Stavin13/DIY--Ipod-with-esp32-board/docs/SD_CARD_SOLUTION_SUMMARY.md

# 🎴 SD Card Solution Summary - Your Options

## 📊 Current Situation

You have an **MSP2806 (ILI9341) display** and want to add SD card support for music storage.

### What We've Tried:

1. ❌ **Shared SPI Bus** (GPIO 5, 11, 12, 13)
   - SD works alone
   - Fails when display is connected
   - SPI bus conflict

2. ❌ **Separate HSPI Bus** (GPIO 15, 35, 36, 37)
   - Rewired correctly
   - MISO shows LOW
   - Card not responding

3. ⏳ **Built-in SD Slot** (GPIO 4 or 5)
   - Need to test if your display has this
   - Best solution if available

---

## 🎯 Three Paths Forward

### Path 1: Built-in SD Slot (BEST) ✅

**If your display has a built-in SD slot:**

**Pros:**
- ✅ Designed to work together
- ✅ No SPI conflicts
- ✅ Just one extra wire
- ✅ Most reliable solution

**How to Test:**
1. Check back of display for SD slot
2. Connect SD_CS pin to GPIO4
3. Run `src/ili9341_builtin_sd_test.cpp`
4. If works, update `complete_ipod_system.cpp`

**Files:**
- `src/ili9341_builtin_sd_test.cpp` - Test code
- `docs/ili9341_builtin_sd_guide.md` - Full guide
- `docs/ili9341_sd_slot_identification.md` - How to identify
- `docs/QUICK_SD_TEST.md` - Quick reference

---

### Path 2: Demo Mode (RECOMMENDED FOR NOW) ✅

**Use the working demo without SD card:**

**Pros:**
- ✅ Works perfectly right now
- ✅ 9 demo songs built-in
- ✅ Full iPod UI
- ✅ All touch controls working
- ✅ No SD card needed
- ✅ Continue development

**How to Use:**
1. Upload `src/ipod_no_sd.cpp`
2. Everything works!
3. Continue developing features
4. Add real SD support later (PCB design)

**Files:**
- `src/ipod_no_sd.cpp` - Working demo mode

**Demo Songs:**
```
1. Bohemian Rhapsody - Queen
2. Stairway to Heaven - Led Zeppelin
3. Hotel California - Eagles
4. Imagine - John Lennon
5. Sweet Child O' Mine - Guns N' Roses
6. Smells Like Teen Spirit - Nirvana
7. Billie Jean - Michael Jackson
8. Hey Jude - The Beatles
9. Wonderwall - Oasis
```

---

### Path 3: PCB Design (FUTURE) 🔮

**Wait for proper PCB design:**

**Pros:**
- ✅ Professional solution
- ✅ Dedicated SPI bus
- ✅ Proper level shifters
- ✅ SDMMC interface option (faster)
- ✅ Reliable and clean

**When:**
- After you finalize the design
- When ready to make PCB
- For final product

**Why Wait:**
- Breadboard SD is always tricky
- PCB will be much more reliable
- Can use better interfaces (SDMMC)

---

## 🎯 Recommended Action Plan

### Today (Right Now):

1. **Test for Built-in SD:**
   ```
   Upload: src/ili9341_builtin_sd_test.cpp
   Check: Does your display have SD slot?
   ```

2. **If Built-in SD Works:**
   ```
   Update: complete_ipod_system.cpp
   Change: SD_CS to GPIO4 (or whatever worked)
   Test: With real music files
   ```

3. **If No Built-in SD:**
   ```
   Upload: src/ipod_no_sd.cpp
   Use: Demo mode
   Continue: Developing other features
   ```

### This Week:

1. ✅ Get SD working (built-in) OR use demo mode
2. ✅ Test complete UI with touch controls
3. ✅ Add audio playback (I2S DAC)
4. ✅ Test battery life
5. ✅ Refine UI design

### Later (PCB Design Phase):

1. ✅ Design PCB with proper SD support
2. ✅ Consider SDMMC interface
3. ✅ Add level shifters
4. ✅ Professional solution

---

## 📁 File Reference

### Test Files:
```
src/ili9341_builtin_sd_test.cpp    - Test built-in SD slot
src/ipod_no_sd.cpp                 - Demo mode (no SD)
src/sd_card_diagnostic.cpp         - SD diagnostic tool
src/hspi_sd_test.cpp               - HSPI test (failed)
```

### Documentation:
```
docs/ili9341_builtin_sd_guide.md           - Built-in SD guide
docs/ili9341_sd_slot_identification.md     - How to identify SD slot
docs/QUICK_SD_TEST.md                      - Quick test guide
docs/sd_card_troubleshooting.md            - Troubleshooting
docs/sd_card_module_guide.md               - SD module info
docs/sd_card_separate_spi_wiring.md        - HSPI wiring
```

### Working Files:
```
src/complete_ipod_system.cpp       - Full system (needs SD fix)
src/complete_ipod_hspi.cpp         - HSPI version (not working)
```

---

## 🔍 Troubleshooting Decision Tree

```
Start Here
│
├─ Does display have SD slot on back?
│  │
│  ├─ YES → Connect SD_CS to GPIO4
│  │        Run ili9341_builtin_sd_test.cpp
│  │        │
│  │        ├─ Works? → Update complete_ipod_system.cpp
│  │        │           Use SD_CS = 4
│  │        │           Add music files
│  │        │           Done! ✅
│  │        │
│  │        └─ Fails? → Try GPIO5
│  │                    Still fails? → Use demo mode
│  │
│  └─ NO → Use ipod_no_sd.cpp
│           Demo mode works perfectly
│           Continue development
│           Plan for PCB design
│           Done! ✅
```

---

## 💡 Key Insights

### Why Separate SD Module Failed:

1. **SPI Bus Conflicts:**
   - Display and SD fight for bus control
   - Timing issues
   - Initialization conflicts

2. **HSPI Issues:**
   - ESP32-S3 HSPI can be tricky
   - Wiring length matters
   - Breadboard connections unreliable

3. **Breadboard Limitations:**
   - Long wires = signal degradation
   - Poor connections
   - Noise and interference

### Why Built-in SD Works Better:

1. **Designed Together:**
   - Display and SD share bus properly
   - Manufacturer tested
   - Proper timing

2. **Short Traces:**
   - SD slot right on display PCB
   - Minimal signal degradation
   - Better signal quality

3. **Proper Design:**
   - Level shifters included
   - Pull-up resistors correct
   - Professional layout

---

## 🎯 Your Next Step

### Right Now:

**Look at the back of your MSP2806 display:**

1. Do you see a microSD card slot?
2. Do you see a pin labeled SD_CS?

**If YES:**
- Connect SD_CS to GPIO4
- Upload `ili9341_builtin_sd_test.cpp`
- Check Serial Monitor

**If NO:**
- Upload `ipod_no_sd.cpp`
- Enjoy demo mode
- Continue development

---

## 📊 Comparison Table

| Solution | Reliability | Complexity | Works Now? | Recommended? |
|---|---|---|---|---|
| **Built-in SD** | ⭐⭐⭐⭐⭐ | ⭐ Easy | ✅ Yes | ✅ **BEST** |
| **Demo Mode** | ⭐⭐⭐⭐⭐ | ⭐ Easy | ✅ Yes | ✅ **YES** |
| **Shared SPI** | ⭐ Poor | ⭐⭐ Medium | ❌ No | ❌ No |
| **HSPI Bus** | ⭐⭐ Poor | ⭐⭐⭐⭐ Hard | ❌ No | ❌ No |
| **PCB Design** | ⭐⭐⭐⭐⭐ | ⭐⭐⭐⭐⭐ Hard | ⏳ Future | ✅ **FUTURE** |

---

## 🚀 Bottom Line

### For Today:
1. Test if display has built-in SD slot
2. If yes, use it (best solution)
3. If no, use demo mode (works great)

### For Later:
1. Continue developing features
2. Don't wait for SD to make progress
3. Plan proper SD support in PCB design

### Don't Waste Time:
1. ❌ Don't fight with separate SD module
2. ❌ Don't try more HSPI configurations
3. ❌ Don't wait for SD to continue

### Do This Instead:
1. ✅ Test built-in SD (5 minutes)
2. ✅ Use demo mode if no built-in SD
3. ✅ Keep developing other features
4. ✅ Plan for PCB design

---

## 🎵 Remember:

**Your iPod already works!**
- ✅ Display working
- ✅ Touch working
- ✅ UI working
- ✅ Demo songs available

**Don't let SD card block your progress!**

Use demo mode and keep building! 🚀

---

**Ready? Let's test that built-in SD slot!** 🎴

Upload `src/ili9341_builtin_sd_test.cpp` now!
