Stavin13/DIY--Ipod-with-esp32-board/docs/ttp229_case_integration.md

# TTP229 Touch Sensor - 3D Case Integration Guide

## 🎯 **Touch-Sensitive iPod Case Design**

This guide shows you how to integrate the TTP229 capacitive touch sensor into your 3D printed iPod case for a sleek, button-less design.

## 📐 **Case Design Modifications**

### **Touch Zone Layout**

```
iPod Case - External View (what user sees):

    ┌─────────────────────────────────────────────────────────────┐
    │                                                             │
    │  [MENU]                                        [PLAY]       │
    │   ●                                              ●          │
    │                                                             │
    │  ┌─────────────────────────────────────────────────────┐   │
    │  │                                                     │   │
    │  │              Display Window                         │   │
    │  │              (240x320px)                           │   │
    │  │                                                     │   │
    │  └─────────────────────────────────────────────────────┘   │
    │                                                             │
    │                      [SELECT]                              │
    │                         ●                                  │
    │                                                             │
    │  [PREV]                                        [NEXT]       │
    │   ●                                              ●          │
    │                                                             │
    └─────────────────────────────────────────────────────────────┘

Touch zones marked with ● - user touches these areas
No physical buttons - smooth case surface
Icons/text printed or engraved on case
```

### **Internal Touch Pad Placement**

```
iPod Case - Internal View (inside case):

    ┌─────────────────────────────────────────────────────────────┐
    │                                                             │
    │  [TP0]                                         [TP1]        │
    │  Copper                                        Copper       │
    │  15x15mm                                       15x15mm      │
    │                                                             │
    │  ┌─────────────────────────────────────────────────────┐   │
    │  │                                                     │   │
    │  │              Display Mounting                       │   │
    │  │                                                     │   │
    │  │                                                     │   │
    │  └─────────────────────────────────────────────────────┘   │
    │                                                             │
    │                    [TP8] Copper                            │
    │                    20x20mm                                 │
    │                                                             │
    │  [TP2]                                         [TP3]        │
    │  Copper                                        Copper       │
    │  15x15mm                                       15x15mm      │
    │                                                             │
    │  [TTP229 Module]  [ESP32-S3]  [Display Connector]         │
    │                                                             │
    └─────────────────────────────────────────────────────────────┘

Copper pads mounted 2-3mm behind case surface
Wires route to TTP229 module
All components secured inside case
```

## 🔧 **Assembly Materials**

### **Required Materials**
```
✅ TTP229 16-channel touch module ($5)
✅ Copper tape (15mm wide, adhesive-backed)
✅ Thin wire (28-30 AWG, 9 pieces x 10cm)
✅ Hot glue gun or double-sided tape
✅ Soldering iron and solder
✅ Wire strippers
✅ Multimeter (for testing)
```

### **Optional Materials**
```
✅ Kapton tape (insulation)
✅ Heat shrink tubing
✅ Cable ties (wire management)
✅ Foam tape (vibration dampening)
```

## 📋 **Step-by-Step Assembly**

### **Step 1: Prepare Touch Pads**

#### **Using Copper Tape (Easiest)**
```
1. Cut copper tape into squares:
   - Menu, Play, Prev, Next: 15mm x 15mm
   - Select: 20mm x 20mm

2. Mark positions inside case:
   - Use case design as template
   - Align with external touch zone markings
   - Ensure 2-3mm behind case surface

3. Apply copper tape:
   - Clean surface with isopropyl alcohol
   - Press firmly to ensure good adhesion
   - Smooth out any air bubbles
   - Leave 5mm tab for wire connection
```

#### **Using PCB Pads (Professional)**
```
1. Design small PCB with copper pads
2. Order from JLCPCB (₹500 for 5 pcs)
3. Mount PCB inside case with standoffs
4. Connect wires to PCB pads
```

### **Step 2: Wire Connections**

```
1. Strip 3mm from each wire end

2. Solder wires to copper pads:
   - Apply flux to copper tape
   - Tin the wire end
   - Solder wire to copper pad tab
   - Insulate with heat shrink or tape

3. Label wires:
   - TP0: Menu
   - TP1: Play
   - TP2: Previous
   - TP3: Next
   - TP8: Select

4. Route wires to TTP229 location:
   - Use wire channels in case design
   - Secure with hot glue or cable ties
   - Keep wires away from display
```

### **Step 3: Connect TTP229 Module**

```
1. Mount TTP229 module:
   - Position near ESP32-S3
   - Use double-sided tape or standoffs
   - Ensure module is secure

2. Connect power:
   - VCC → ESP32-S3 3.3V
   - GND → ESP32-S3 GND

3. Connect I2C:
   - SDA → ESP32-S3 GPIO21
   - SCL → ESP32-S3 GPIO22

4. Connect touch pads:
   - Solder wires to TP0-TP8 pads
   - Use multimeter to verify connections
   - Check for shorts between pads
```

### **Step 4: Testing Before Assembly**

```
1. Power on ESP32-S3

2. Upload test code:
   - Use src/ttp229_touch_test.cpp
   - Open Serial Monitor (115200 baud)

3. Test each touch pad:
   - Touch copper pad with finger
   - Verify detection in Serial Monitor
   - Check all 5 pads work correctly

4. Test through case material:
   - Place case top over pads (2-3mm gap)
   - Touch external surface
   - Verify detection still works
   - Adjust sensitivity if needed
```

### **Step 5: Final Assembly**

```
1. Secure all components:
   - ESP32-S3 in mounting bracket
   - Display in mounting frame
   - TTP229 module secured
   - All wires organized

2. Close case:
   - Align top and bottom shells
   - Ensure no wire pinching
   - Snap or screw together

3. Final testing:
   - Upload full iPod interface code
   - Test all touch zones
   - Verify display works
   - Check for false touches
```

## 🎨 **Case Surface Finishing**

### **Marking Touch Zones**

#### **Option 1: Printed Icons**
```
1. Design icons in vector software
2. Print on vinyl sticker paper
3. Apply to case surface over touch zones
4. Clear coat for protection
```

#### **Option 2: Engraved Labels**
```
1. Use laser engraver or CNC
2. Engrave icons/text on case surface
3. Fill with contrasting paint
4. Clear coat for durability
```

#### **Option 3: Embedded Icons**
```
1. Pause 3D print at surface layer
2. Insert different color filament
3. Resume print (multi-color effect)
4. Icons embedded in case
```

### **Recommended Icons**
```
Menu:     ☰ (hamburger menu)
Play:     ▶ (play triangle)
Previous: ⏮ (skip back)
Next:     ⏭ (skip forward)
Select:   ● (circle) or ✓ (checkmark)
```

## 🔧 **Troubleshooting**

### **Touch Not Detected**
```
Problem: No response when touching
Solutions:
1. Check TTP229 I2C connection
2. Verify copper pad connections
3. Reduce case thickness (try 2mm)
4. Increase copper pad size
5. Ensure good ground connection
```

### **False Touches**
```
Problem: Random touch detection
Solutions:
1. Add ground plane around pads
2. Increase spacing between pads
3. Shield wires with grounded foil
4. Add debouncing in code
5. Calibrate TTP229 (power cycle)
```

### **Weak Sensitivity**
```
Problem: Need to press hard
Solutions:
1. Larger copper pads (20mm x 20mm)
2. Thinner case material (2mm)
3. Better ground connection
4. Clean case surface (no oils)
5. Use copper instead of aluminum
```

### **Inconsistent Response**
```
Problem: Sometimes works, sometimes doesn't
Solutions:
1. Check wire connections (re-solder)
2. Secure copper pads (re-apply)
3. Add pull-up resistors on I2C
4. Shield from EMI sources
5. Power supply stability
```

## 📐 **Case Design Specifications**

### **Touch Zone Dimensions**
```
Case Thickness: 2-3mm (optimal for touch)
Touch Pad Size: 15mm x 15mm (minimum)
Pad Spacing: 3mm minimum between pads
Surface Finish: Smooth (no texture over pads)
Material: PLA or ABS (both work well)
```

### **Internal Clearances**
```
Copper pad to case: 2-3mm gap
Wire routing channels: 3mm wide x 2mm deep
TTP229 module space: 25mm x 20mm x 5mm
Component clearance: 2mm minimum
```

## 💡 **Design Tips**

### **For Best Touch Sensitivity**
```
✅ Use 2-3mm case thickness
✅ Smooth external surface
✅ Large copper pads (15mm+)
✅ Good ground plane
✅ Clean, dry surface
```

### **For Reliable Operation**
```
✅ Secure all connections
✅ Strain relief on wires
✅ Shield from EMI
✅ Proper wire routing
✅ Test before final assembly
```

### **For Professional Appearance**
```
✅ Clean wire routing
✅ Labeled touch zones
✅ Consistent pad spacing
✅ Hidden components
✅ Smooth case finish
```

## 🎯 **Advantages of This Design**

### **vs Physical Buttons**
```
✅ No holes in case (waterproof)
✅ No mechanical wear
✅ Sleek, modern look
✅ Easier to clean
✅ More reliable long-term
✅ Cheaper to manufacture
```

### **vs Touch Screen**
```
✅ Works through case material
✅ No calibration needed
✅ Better for music control
✅ Lower power consumption
✅ More durable
✅ Cheaper overall
```

## 📊 **Cost Breakdown**

```
TTP229 module:      $5 (₹400)
Copper tape:        $2 (₹150)
Wire (9 pieces):    $1 (₹80)
Solder/supplies:    $2 (₹150)
Case material:      $5 (₹400)

Total: $15 (₹1,180)

Much cheaper than:
- Haptic system: $25 (₹1,960)
- Touch display: $40+ (₹3,200+)
```

## 🚀 **Next Steps**

1. **Test TTP229** - Upload test code, verify I2C
2. **Prepare pads** - Cut copper tape, mark positions
3. **Wire connections** - Solder wires to pads
4. **Test through case** - Verify touch detection
5. **Final assembly** - Secure everything, close case
6. **Upload full code** - Complete iPod interface

This touch-sensitive design gives you a **modern, sleek iPod** with no physical buttons - just smooth touch zones that work through your 3D printed case! 🎵

The TTP229 was actually a **better choice** than the haptic driver - it's simpler, cheaper, and gives you that premium touch-sensitive interface. Great purchase! 👍
