Stavin13/DIY--Ipod-with-esp32-board/docs/touchscreen_wiring_diagram.md

# Touchscreen iPod Wiring Diagram - ESP32-S3

## Simplified System Layout (No Rotary Encoder)

```
                    ┌─────────────────────────────────────────┐
                    │           ESP32-S3-N16R8                │
                    │                                         │
                    │  ┌─────┐                               │
                    │  │USB-C│                               │
                    │  └─────┘                               │
                    │                                         │
    ┌───────────────┼─ GPIO10 (TFT_CS)                       │
    │   ┌───────────┼─ GPIO9  (TFT_DC)                       │
    │   │   ┌───────┼─ GPIO8  (TFT_RST)                      │
    │   │   │   ┌───┼─ GPIO11 (TFT_MOSI)                     │
    │   │   │   │ ┌─┼─ GPIO12 (TFT_SCLK)                     │
    │   │   │   │ │ └─ GPIO13 (TFT_MISO)                     │
    │   │   │   │ │                                           │
    │   │   │   │ │   ┌───────┼─ GPIO6  (TOUCH_CS)           │
    │   │   │   │ │   │   ┌───┼─ GPIO7  (TOUCH_CLK)          │
    │   │   │   │ │   │   │ ┌─┼─ GPIO5  (TOUCH_DIN)          │
    │   │   │   │ │   │   │ │ └─ GPIO4  (TOUCH_DO)           │
    │   │   │   │ │   │   │ │                                 │
    │   │   │   │ │   │   │ │   ┌───────┼─ GPIO35 (SD_CS)    │
    │   │   │   │ │   │   │ │   │   ┌───┼─ GPIO36 (SD_MOSI)  │
    │   │   │   │ │   │   │ │   │   │ ┌─┼─ GPIO37 (SD_MISO)  │
    │   │   │   │ │   │   │ │   │   │ │ └─ GPIO38 (SD_SCLK)  │
    │   │   │   │ │   │   │ │   │   │ │                       │
    │   │   │   │ │   │   │ │   │   │ │ ┌─────────┼─ 3.3V     │
    │   │   │   │ │   │   │ │   │   │ │ │     ┌───┼─ GND      │
    └───┼───┼───┼─┼───┼───┼─┼───┼───┼─┼─┼─────┼───┼───────────┘
        │   │   │ │   │   │ │   │   │ │ │     │   │
        │   │   │ │   │   │ │   │   │ │ │     │   │
    ┌───▼───▼───▼─▼───▼───▼─▼───┐   │ │ │     │   │
    │  2.8" ILI9341 TFT Display │   │ │ │     │   │
    │  ┌─────────────────────┐   │   │ │ │     │   │
    │  │                     │   │   │ │ │     │   │
    │  │     240 x 320       │   │   │ │ │     │   │
    │  │  TOUCHSCREEN iPod   │   │   │ │ │     │   │
    │  │                     │   │   │ │ │     │   │
    │  │  🎵 Tap to Control  │   │   │ │ │     │   │
    │  │  👆 Swipe to Browse │   │   │ │ │     │   │
    │  └─────────────────────┘   │   │ │ │     │   │
    │                            │   │ │ │     │   │
    │ CS DC RST MOSI SCLK MISO   │   │ │ │     │   │
    │ │  │  │   │    │    │      │   │ │ │     │   │
    │ │  │  │   │    │    │      │   │ │ │     │   │
    │ T_CS T_CLK T_DIN T_DO      │   │ │ │     │   │
    │ │    │     │     │         │   │ │ │     │   │
    └─┼────┼─────┼─────┼─────────┘   │ │ │     │   │
      │    │     │     │             │ │ │     │   │
      └────┼─────┼─────┼─────────────┘ │ │     │   │
           └─────┼─────┼───────────────┘ │     │   │
                 └─────┼─────────────────┘     │   │
                       └───────────────────────┘   │
                                                   │
                       ┌───────────────────────────┘
                       │
                   ┌───▼───────┐
                   │ SD Card   │
                   │ Module    │
                   │           │
                   │ 💾 Music  │
                   │ Storage   │
                   │           │
                   │ CS MOSI   │
                   │ MISO SCLK │
                   │ VCC GND   │
                   └───────────┘
```

## Touch Interface Features

### 🎵 Music Control Gestures:
- **Tap**: Play/Pause, Select
- **Swipe Left**: Next Track
- **Swipe Right**: Previous Track  
- **Swipe Up**: Volume Up
- **Swipe Down**: Volume Down
- **Long Press**: Context Menu
- **Pinch**: Zoom (for album art)

### 📱 Navigation:
- **Home Screen**: Library, Now Playing, Settings
- **Library**: Artists, Albums, Songs, Playlists
- **Now Playing**: Track info, controls, progress
- **Settings**: Volume, EQ, Display, Power

## Connection Summary

### 🔌 Power (Shared by All):
```
ESP32-S3    →    All Modules
3.3V        →    VCC (Display, Touch, SD Card)
GND         →    GND (Display, Touch, SD Card)
```

### 📺 Display + Touch (Single Module):
```
ESP32-S3    →    ILI9341 + Touch
GPIO10      →    CS (Display)
GPIO9       →    DC (Display)
GPIO8       →    RST (Display)
GPIO11      →    MOSI (Display)
GPIO12      →    SCLK (Display)
GPIO13      →    MISO (Display)
GPIO6       →    T_CS (Touch)
GPIO7       →    T_CLK (Touch)
GPIO5       →    T_DIN (Touch)
GPIO4       →    T_DO (Touch)
```

### 💾 Storage:
```
ESP32-S3    →    SD Card Module
GPIO35      →    CS
GPIO36      →    MOSI
GPIO37      →    MISO
GPIO38      →    SCLK
```

## Available Pins for Expansion

### 🔘 Optional Hardware Buttons:
- **GPIO0**: Menu/Back button (Boot pin)
- **GPIO1**: Volume Up button
- **GPIO2**: Volume Down button

### 🔧 Future Features:
- **GPIO14-16**: I2C devices (accelerometer, gyroscope)
- **GPIO40-48**: LEDs, additional sensors
- **GPIO17-22**: USB-C audio and power management

## Benefits of Touch-Only Design

### ✅ Advantages:
- **Modern Interface**: iPhone-like experience
- **Fewer Components**: No rotary encoder needed
- **More Pins Available**: 3 extra GPIO pins
- **Gesture Support**: Swipe, pinch, long press
- **Visual Feedback**: On-screen controls
- **Easier Assembly**: Fewer wires to connect

### 🎯 Perfect For:
- **Music Browsing**: Touch scrolling through lists
- **Album Art**: Full-screen display with touch controls
- **Playlists**: Drag and drop organization
- **Settings**: Touch-friendly menus
- **Games**: Touch-based mini-games while music plays

This touchscreen design gives you a modern, iPhone-like music player experience!
