Stavin13/DIY--Ipod-with-esp32-board/docs/ttp229_keypad_module_guide.md

# TTP229 16-Key Capacitive Touch Keypad Module - iPod Integration

## 🎯 **Your Specific Module**

You have the **TTP229-BSF 16-channel capacitive touch keypad module** with built-in touch pads. This is perfect for your iPod project!

### **Module Features**
```
✅ 16 pre-made touch pads (numbered 1-16)
✅ Built-in TTP229-BSF IC
✅ I2C interface (easy connection)
✅ 3.3V compatible
✅ No external components needed
✅ Ready to use out of the box
```

## 🔌 **Module Pinout**

### **Pin Configuration**
```
Top Header Pins (looking at module):

Pin 1:  VCC   - Power (3.3V)
Pin 2:  GND   - Ground
Pin 3:  SCL   - I2C Clock
Pin 4:  SDO   - Serial Data Out (I2C mode: SDA)

Note: In I2C mode, SDO becomes SDA
```

### **Touch Pad Layout**
```
Your module has 16 touch pads arranged in 4x4 grid:

Row 1:  [1]  [2]  [3]  [4]
Row 2:  [5]  [6]  [7]  [8]
Row 3:  [9]  [10] [11] [12]
Row 4:  [13] [14] [15] [16]

Each pad is a capacitive touch sensor
Touch detection works through thin plastic/acrylic
```

## 🔧 **Wiring to ESP32-S3**

### **Simple 4-Wire Connection**

```
TTP229 Module    →    ESP32-S3
--------------         --------
VCC (Pin 1)      →    3.3V
GND (Pin 2)      →    GND
SCL (Pin 3)      →    GPIO22 (I2C Clock)
SDO (Pin 4)      →    GPIO21 (I2C Data/SDA)
```

### **Breadboard Wiring Diagram**

```
ESP32-S3 DevKit:                    TTP229 Module:

     [USB-C]                        [Header Pins]
   ┌─────────────┐                 ┌──────────────┐
   │             │                 │ VCC GND SCL SDO
   │             │                 │  │   │   │   │
   │        3.3V │─────────────────┘  │   │   │
   │         GND │────────────────────┘   │   │
   │        IO22 │────────────────────────┘   │
   │        IO21 │────────────────────────────┘
   │             │
   │             │                 ┌──────────────┐
   │             │                 │  1   2   3   4
   │             │                 │  5   6   7   8
   │             │                 │  9  10  11  12
   │             │                 │ 13  14  15  16
   └─────────────┘                 └──────────────┘
                                   Touch Pads (4x4)
```

## 💻 **Test Code for Your Module**

### **Basic Touch Test**

```cpp
/*
ESP32-S3 + TTP229 16-Key Touch Keypad Test
Tests all 16 touch pads on your module
*/

#include <Wire.h>

// TTP229 I2C Configuration
#define TTP229_ADDR 0x57
#define I2C_SDA 21
#define I2C_SCL 22

uint16_t touchStatus = 0;
uint16_t lastTouchStatus = 0;

void setup() {
  Serial.begin(115200);
  delay(2000);
  
  Serial.println("╔════════════════════════════════════════╗");
  Serial.println("║   TTP229 16-Key Touch Keypad Test     ║");
  Serial.println("║        ESP32-S3 Integration           ║");
  Serial.println("╚════════════════════════════════════════╝");
  Serial.println();
  
  // Initialize I2C
  Wire.begin(I2C_SDA, I2C_SCL);
  Wire.setClock(100000); // 100kHz
  
  Serial.print("🔌 I2C initialized - SDA: GPIO");
  Serial.print(I2C_SDA);
  Serial.print(", SCL: GPIO");
  Serial.println(I2C_SCL);
  
  // Test connection
  testConnection();
  
  Serial.println("🎯 Touch keypad ready!");
  Serial.println("   Touch any pad (1-16) to test...");
  Serial.println();
  
  // Show keypad layout
  printKeypadLayout();
}

void loop() {
  // Read touch status
  touchStatus = readTTP229();
  
  // Check for changes
  if (touchStatus != lastTouchStatus) {
    handleTouchChange();
    lastTouchStatus = touchStatus;
  }
  
  delay(50); // 20Hz polling
}

void testConnection() {
  Serial.println("🔍 Testing TTP229 connection...");
  
  Wire.beginTransmission(TTP229_ADDR);
  uint8_t error = Wire.endTransmission();
  
  if (error == 0) {
    Serial.println("✅ TTP229 module found!");
    Serial.println("   Address: 0x57");
  } else {
    Serial.print("❌ Module not found! Error: ");
    Serial.println(error);
    Serial.println();
    Serial.println("Check wiring:");
    Serial.println("  VCC → 3.3V");
    Serial.println("  GND → GND");
    Serial.println("  SCL → GPIO22");
    Serial.println("  SDO → GPIO21");
  }
  Serial.println();
}

uint16_t readTTP229() {
  Wire.requestFrom(TTP229_ADDR, 2);
  
  if (Wire.available() >= 2) {
    uint8_t lowByte = Wire.read();
    uint8_t highByte = Wire.read();
    return (highByte << 8) | lowByte;
  }
  
  return 0;
}

void handleTouchChange() {
  // Check each key (1-16)
  for (int i = 0; i < 16; i++) {
    bool currentState = (touchStatus >> i) & 0x01;
    bool lastState = (lastTouchStatus >> i) & 0x01;
    
    if (currentState && !lastState) {
      // Key pressed
      Serial.print("👆 Key ");
      Serial.print(i + 1);
      Serial.println(" pressed");
      
      // Show visual grid
      printTouchGrid();
    }
  }
}

void printKeypadLayout() {
  Serial.println("📋 Keypad Layout:");
  Serial.println("   ┌────┬────┬────┬────┐");
  Serial.println("   │ 1  │ 2  │ 3  │ 4  │");
  Serial.println("   ├────┼────┼────┼────┤");
  Serial.println("   │ 5  │ 6  │ 7  │ 8  │");
  Serial.println("   ├────┼────┼────┼────┤");
  Serial.println("   │ 9  │ 10 │ 11 │ 12 │");
  Serial.println("   ├────┼────┼────┼────┤");
  Serial.println("   │ 13 │ 14 │ 15 │ 16 │");
  Serial.println("   └────┴────┴────┴────┘");
  Serial.println();
}

void printTouchGrid() {
  Serial.println("Current touches:");
  Serial.print("   ");
  
  for (int i = 0; i < 16; i++) {
    if ((touchStatus >> i) & 0x01) {
      Serial.print("[");
      if (i + 1 < 10) Serial.print(" ");
      Serial.print(i + 1);
      Serial.print("] ");
    } else {
      Serial.print(" --  ");
    }
    
    if ((i + 1) % 4 == 0) {
      Serial.println();
      Serial.print("   ");
    }
  }
  Serial.println();
}
```

Save as: `src/ttp229_keypad_test.cpp`

## 🎮 **iPod Button Mapping**

### **Recommended Key Assignment**

```
Your 16-key module mapped to iPod controls:

┌────────────────────────────────────┐
│  [1]      [2]      [3]      [4]   │
│  Menu     Up      Play     Vol+   │
│                                    │
│  [5]      [6]      [7]      [8]   │
│  Left    Select   Right    Vol-   │
│                                    │
│  [9]      [10]     [11]     [12]  │
│  Prev     Down     Next    Shuffle│
│                                    │
│  [13]     [14]     [15]     [16]  │
│  Repeat   EQ      Playlist  Lock  │
└────────────────────────────────────┘

Primary Controls (Keys 1-12):
- Key 1:  Menu/Back
- Key 2:  Navigate Up
- Key 3:  Play/Pause
- Key 4:  Volume Up
- Key 5:  Navigate Left
- Key 6:  Select/OK
- Key 7:  Navigate Right
- Key 8:  Volume Down
- Key 9:  Previous Track
- Key 10: Navigate Down
- Key 11: Next Track
- Key 12: Shuffle

Secondary Controls (Keys 13-16):
- Key 13: Repeat Mode
- Key 14: Equalizer
- Key 15: Playlist
- Key 16: Screen Lock
```

### **Simplified 5-Button iPod Mode**

```
If you only want classic iPod controls:

┌────────────────────────────────────┐
│  [1]      [2]      [3]      [4]   │
│  Menu     Up      Play     --     │
│                                    │
│  [5]      [6]      [7]      [8]   │
│  Left    Select   Right    --     │
│                                    │
│  [9]      [10]     [11]     [12]  │
│  Prev     Down     Next     --    │
│                                    │
│  [13]     [14]     [15]     [16]  │
│  --       --       --       --    │
└────────────────────────────────────┘

Use only keys 1,2,3,5,6,7,9,10,11
(Classic iPod click wheel simulation)
```

## 🎨 **Mounting Options**

### **Option 1: Direct Module Mount (Easiest)**

```
Mount the entire module inside your case:

Advantages:
✅ No additional wiring needed
✅ All 16 keys available
✅ Easy to test and debug
✅ Can touch through thin case top

Steps:
1. Create cutout in case for module
2. Mount module with standoffs
3. Cover with thin acrylic/plastic (2mm)
4. Label keys on case surface
```

### **Option 2: External Touch Pads**

```
Use module's IC, create custom touch pads:

Steps:
1. Desolder the touch pads from module (advanced)
2. Create custom copper pad layout
3. Wire custom pads to module IC
4. Mount in your case design

Advantages:
✅ Custom button layout
✅ Fits your case design
✅ Professional appearance

Disadvantages:
❌ Requires desoldering skills
❌ More complex assembly
❌ Risk of damaging module
```

### **Option 3: Case Overlay (Recommended)**

```
Keep module intact, add case overlay:

Steps:
1. Mount module inside case
2. Create 2-3mm acrylic/plastic overlay
3. Mark button positions on overlay
4. Touch works through overlay

Advantages:
✅ Module stays intact
✅ Easy to assemble
✅ Waterproof
✅ Professional look
```

## 📐 **Case Integration Design**

### **Module Dimensions**
```
PCB Size: ~70mm x 70mm
Touch Pad Size: ~15mm x 15mm each
Pad Spacing: ~2mm between pads
Thickness: ~2mm PCB + 3mm components
Total Height: ~5mm
```

### **Case Cutout Design**
```
Create recess in case:
- Width: 72mm (module + 1mm clearance)
- Height: 72mm (module + 1mm clearance)
- Depth: 6mm (module + 1mm clearance)

Overlay thickness: 2-3mm plastic/acrylic
Touch sensitivity: Works through 2-3mm material
```

## 🔧 **Assembly Instructions**

### **Step 1: Test Module**
```
1. Connect 4 wires to ESP32-S3
2. Upload test code
3. Touch each pad (1-16)
4. Verify all pads work
5. Check Serial Monitor output
```

### **Step 2: Mount in Case**
```
1. Create mounting holes for standoffs
2. Secure module with M2.5 screws
3. Ensure module is level
4. Leave space for wiring
```

### **Step 3: Add Overlay**
```
1. Cut 2-3mm acrylic to size
2. Mark button positions
3. Add labels/icons
4. Secure over module
5. Test touch through overlay
```

### **Step 4: Final Assembly**
```
1. Connect display
2. Upload full iPod code
3. Test all functions
4. Close case
5. Enjoy your touch iPod!
```

## 💡 **Pro Tips**

### **For Best Touch Sensitivity**
```
✅ Use 2-3mm overlay thickness
✅ Clean, smooth surface
✅ Avoid air gaps between module and overlay
✅ Use acrylic or PLA (not ABS if too thick)
✅ Keep fingers dry for best response
```

### **For Reliable Operation**
```
✅ Secure all wire connections
✅ Use proper I2C pull-ups (usually built-in)
✅ Keep module away from high-voltage traces
✅ Add debouncing in code (50ms)
✅ Power from stable 3.3V source
```

### **For Professional Appearance**
```
✅ Print/engrave button labels
✅ Use consistent spacing
✅ Add LED indicators (optional)
✅ Smooth case finish
✅ Color-code important buttons
```

## 🎯 **Advantages of Your Module**

### **vs Separate Components**
```
✅ Pre-assembled (no soldering IC)
✅ All 16 channels ready to use
✅ Built-in touch pads
✅ Tested and working
✅ Easy to prototype
✅ Cheap ($5 vs $15+ for parts)
```

### **vs Physical Buttons**
```
✅ No mechanical wear
✅ Waterproof (sealed case)
✅ Modern touch interface
✅ More reliable long-term
✅ Easier case design
✅ Sleek appearance
```

## 📊 **Quick Start Checklist**

```
□ Connect VCC to ESP32-S3 3.3V
□ Connect GND to ESP32-S3 GND
□ Connect SCL to ESP32-S3 GPIO22
□ Connect SDO to ESP32-S3 GPIO21
□ Upload ttp229_keypad_test.cpp
□ Open Serial Monitor (115200 baud)
□ Touch pads 1-16 to test
□ Verify all pads respond
□ Plan button layout for iPod
□ Design case mounting
□ Create overlay if needed
□ Upload full iPod interface
□ Test complete system
□ Assemble in case
□ Enjoy your touch iPod!
```

## 🚀 **Next Steps**

1. **Wire it up** - 4 simple connections
2. **Test it** - Upload test code, touch all 16 pads
3. **Plan layout** - Decide which keys for which functions
4. **Design case** - Create mounting and overlay
5. **Full integration** - Upload complete iPod code

Your TTP229 module is **perfect for this project** - it has everything you need built-in, and at $5 it's an incredible value! The 16 keys give you plenty of options for a full-featured iPod interface. 🎵

Would you like me to create the complete iPod interface code specifically for your 16-key layout?
