Stavin13/DIY--Ipod-with-esp32-board/docs/ttp229_touch_sensor_guide.md

# TTP229 16-Channel Touch Sensor - ESP32-S3 iPod Integration

## 🎯 **TTP229 Overview**

The TTP229 is a **capacitive touch sensor IC** that can detect touch through non-conductive materials like plastic, glass, or acrylic. This is perfect for your iPod project - you can create touch-sensitive areas on your 3D printed case without physical buttons!

### **Key Features**
```
✅ 16 independent touch keys
✅ Capacitive sensing (works through plastic)
✅ I2C or serial interface
✅ Adjustable sensitivity
✅ Low power consumption
✅ 3.3V compatible
✅ No mechanical wear (no moving parts)
```

### **Advantages for iPod Project**
```
✅ Touch-sensitive case surface
✅ No button holes needed in case
✅ Sleek, modern design
✅ Waterproof (sealed case)
✅ No mechanical failure
✅ Multiple touch zones possible
✅ Gesture detection capable
```

## 🔌 **TTP229 Module Specifications**

### **Module Pinout**
```
TTP229-BSF Module (Common variant):

Power:
- VCC: 3.3V-5V (use 3.3V for ESP32-S3)
- GND: Ground

Communication (I2C Mode):
- SCL: I2C Clock
- SDA: I2C Data

Communication (Serial Mode):
- SDO: Serial Data Output
- SCL: Serial Clock

Touch Pads:
- TP0-TP15: 16 touch input pads
```

### **Operating Modes**

#### **Mode 1: I2C Interface (Recommended)**
```
Address: 0x57 (default)
Speed: 100kHz-400kHz
Data: 16-bit touch status
Advantages:
✅ Easy to use
✅ Standard I2C library
✅ Multiple devices on same bus
✅ Less GPIO pins needed
```

#### **Mode 2: Serial Interface**
```
Clock: External clock on SCL
Data: Serial output on SDO
Advantages:
✅ Faster response
✅ No I2C conflicts
❌ More complex code
```

## 🔧 **Wiring Diagram**

### **ESP32-S3 to TTP229 (I2C Mode)**

```
ESP32-S3    →    TTP229 Module
--------         --------------
3.3V        →    VCC
GND         →    GND
GPIO21      →    SDA (I2C Data)
GPIO22      →    SCL (I2C Clock)
```

### **Touch Pad Layout for iPod**

```
TTP229 Touch Pads Assignment:

TP0:  Menu Button (top-left)
TP1:  Play/Pause Button (top-right)
TP2:  Previous Track (bottom-left)
TP3:  Next Track (bottom-right)
TP4:  Volume Up (side)
TP5:  Volume Down (side)
TP6:  Scroll Up (gesture area)
TP7:  Scroll Down (gesture area)
TP8:  Select/OK (center)
TP9-TP15: Reserved for future features
```

### **Complete System Wiring**

```
ESP32-S3 DevKit Full Wiring:

     [USB-C]
   ┌─────────────┐
   │ 3V3     GND │ ← Power rails
   │ EN      IO0 │
   │ IO36    IO1 │
   │ IO37    IO2 │
   │ IO38    IO3 │
   │ IO39    IO4 │
   │ IO40    IO5 │
   │ IO41    IO6 │
   │ IO42    IO7 │
   │ RXD0    IO8 │ ← Display RST
   │ TXD0    IO9 │ ← Display DC
   │ IO44   IO10 │ ← Display CS
   │ IO43   IO11 │ ← Display MOSI
   │ IO44   IO12 │ ← Display SCLK
   │ IO45   IO13 │ ← Display MISO
   │ IO46   IO14 │
   │ IO47   IO15 │
   │ IO48   IO16 │
   │        IO17 │
   │        IO18 │
   │        IO19 │
   │        IO20 │
   │        IO21 │ ← TTP229 SDA
   │        IO22 │ ← TTP229 SCL
   │        5V   │
   │        GND  │
   └─────────────┘

Display (MSP2806):
GPIO8-13 → Display pins (as before)

TTP229 Touch Sensor:
GPIO21-22 → I2C connection
TP0-TP15 → Touch pads (copper areas)
```

## 📐 **Touch Pad Design**

### **Creating Touch Pads**

#### **Option 1: PCB Touch Pads**
```
Material: Copper on PCB
Size: 10mm x 10mm minimum
Shape: Square, circle, or custom
Spacing: 2-3mm between pads
Connection: Thin trace to TTP229

Advantages:
✅ Professional appearance
✅ Consistent sensitivity
✅ Easy to manufacture
✅ Durable
```

#### **Option 2: Copper Tape**
```
Material: Adhesive copper tape
Size: 15mm x 15mm
Placement: Inside case, behind plastic
Connection: Wire to TTP229 pads

Advantages:
✅ Easy prototyping
✅ Adjustable placement
✅ No PCB needed
✅ Cheap
```

#### **Option 3: Aluminum Foil**
```
Material: Aluminum foil
Size: 20mm x 20mm
Placement: Inside case
Connection: Wire soldered to foil

Advantages:
✅ Readily available
✅ Very cheap
✅ Easy to cut custom shapes
❌ Less durable
```

### **Touch Pad Placement in Case**

```
iPod Case Top View (Internal):

    ┌─────────────────────────────────────────────────────────────┐
    │                                                             │
    │  [TP0]                                          [TP1]       │
    │  Menu                                           Play        │
    │                                                             │
    │  ┌─────────────────────────────────────────────────────┐   │
    │  │                                                     │   │
    │  │              Display Window                         │   │
    │  │              (240x320px)                           │   │
    │  │                                                     │   │
    │  └─────────────────────────────────────────────────────┘   │
    │                                                             │
    │                    [TP8] Select                            │
    │                                                             │
    │  [TP2]                                          [TP3]       │
    │  Previous                                       Next        │
    │                                                             │
    └─────────────────────────────────────────────────────────────┘

Touch pads are placed INSIDE the case, behind 2-3mm plastic.
User touches the OUTSIDE of the case, sensor detects through plastic.
```

### **Sensitivity Adjustment**

```
Touch Sensitivity Factors:
1. Plastic thickness: 2-3mm works best
2. Pad size: Larger = more sensitive
3. Pad material: Copper > Aluminum > Foil
4. Grounding: Good ground improves sensitivity
5. Calibration: TTP229 auto-calibrates on power-up

Optimal Settings:
- Plastic thickness: 2-3mm ABS or PLA
- Pad size: 15mm x 15mm
- Pad spacing: 3mm minimum
- Ground plane: Connect to ESP32-S3 GND
```

## 💻 **Arduino Code**

### **Basic TTP229 Test Code**

```cpp
/*
ESP32-S3 + TTP229 Touch Sensor Test
I2C interface for 16-channel capacitive touch
*/

#include <Wire.h>

// TTP229 I2C Configuration
#define TTP229_ADDR 0x57
#define I2C_SDA 21
#define I2C_SCL 22

// Touch button mapping
#define TOUCH_MENU     0   // TP0
#define TOUCH_PLAY     1   // TP1
#define TOUCH_PREV     2   // TP2
#define TOUCH_NEXT     3   // TP3
#define TOUCH_VOL_UP   4   // TP4
#define TOUCH_VOL_DOWN 5   // TP5
#define TOUCH_SCROLL_UP   6   // TP6
#define TOUCH_SCROLL_DOWN 7   // TP7
#define TOUCH_SELECT   8   // TP8

uint16_t touchStatus = 0;
uint16_t lastTouchStatus = 0;

void setup() {
  Serial.begin(115200);
  delay(2000);
  
  Serial.println("╔════════════════════════════════════════╗");
  Serial.println("║    ESP32-S3 + TTP229 Touch Sensor     ║");
  Serial.println("║      16-Channel Capacitive Touch      ║");
  Serial.println("╚════════════════════════════════════════╝");
  Serial.println();
  
  // Initialize I2C
  Wire.begin(I2C_SDA, I2C_SCL);
  Wire.setClock(100000); // 100kHz for TTP229
  
  Serial.print("🔌 I2C initialized - SDA: GPIO");
  Serial.print(I2C_SDA);
  Serial.print(", SCL: GPIO");
  Serial.println(I2C_SCL);
  
  // Test TTP229 connection
  testTTP229Connection();
  
  Serial.println("🎯 Touch sensor ready!");
  Serial.println("   Touch any pad to test...");
  Serial.println();
}

void loop() {
  // Read touch status
  touchStatus = readTTP229();
  
  // Check for touch changes
  if (touchStatus != lastTouchStatus) {
    handleTouchChange();
    lastTouchStatus = touchStatus;
  }
  
  delay(50); // 20Hz polling rate
}

void testTTP229Connection() {
  Serial.println("🔍 Testing TTP229 connection...");
  
  Wire.beginTransmission(TTP229_ADDR);
  uint8_t error = Wire.endTransmission();
  
  if (error == 0) {
    Serial.println("✅ TTP229 found at address 0x57");
  } else {
    Serial.print("❌ TTP229 not found! I2C error: ");
    Serial.println(error);
    Serial.println("   Check connections:");
    Serial.println("   - VCC to 3.3V");
    Serial.println("   - GND to GND");
    Serial.print("   - SDA to GPIO");
    Serial.println(I2C_SDA);
    Serial.print("   - SCL to GPIO");
    Serial.println(I2C_SCL);
  }
  Serial.println();
}

uint16_t readTTP229() {
  Wire.requestFrom(TTP229_ADDR, 2);
  
  if (Wire.available() >= 2) {
    uint8_t lowByte = Wire.read();
    uint8_t highByte = Wire.read();
    return (highByte << 8) | lowByte;
  }
  
  return 0;
}

void handleTouchChange() {
  // Check each touch pad
  for (int i = 0; i < 16; i++) {
    bool currentState = (touchStatus >> i) & 0x01;
    bool lastState = (lastTouchStatus >> i) & 0x01;
    
    if (currentState && !lastState) {
      // Touch detected
      handleTouchPress(i);
    } else if (!currentState && lastState) {
      // Touch released
      handleTouchRelease(i);
    }
  }
}

void handleTouchPress(int pad) {
  Serial.print("👆 Touch detected on pad ");
  Serial.print(pad);
  Serial.print(" (TP");
  Serial.print(pad);
  Serial.print("): ");
  
  switch (pad) {
    case TOUCH_MENU:
      Serial.println("MENU");
      break;
    case TOUCH_PLAY:
      Serial.println("PLAY/PAUSE");
      break;
    case TOUCH_PREV:
      Serial.println("PREVIOUS");
      break;
    case TOUCH_NEXT:
      Serial.println("NEXT");
      break;
    case TOUCH_VOL_UP:
      Serial.println("VOLUME UP");
      break;
    case TOUCH_VOL_DOWN:
      Serial.println("VOLUME DOWN");
      break;
    case TOUCH_SCROLL_UP:
      Serial.println("SCROLL UP");
      break;
    case TOUCH_SCROLL_DOWN:
      Serial.println("SCROLL DOWN");
      break;
    case TOUCH_SELECT:
      Serial.println("SELECT");
      break;
    default:
      Serial.print("Reserved (");
      Serial.print(pad);
      Serial.println(")");
      break;
  }
}

void handleTouchRelease(int pad) {
  Serial.print("🔓 Touch released on pad ");
  Serial.println(pad);
}
```

Save this as: `src/ttp229_touch_test.cpp`

### **Integrated iPod Interface with TTP229**

I'll create the full iPod interface code in the next file...

## 🎨 **3D Case Design Integration**

### **Case Modifications for Touch Pads**

```
Internal Touch Pad Mounting:
1. Create recesses for copper pads (0.5mm deep)
2. Position pads 2-3mm behind case surface
3. Add wire routing channels
4. Secure pads with adhesive or clips
5. Connect wires to TTP229 module

External Case Surface:
1. Smooth surface (no texture over touch areas)
2. Mark touch zones with icons/text
3. Optional: LED indicators for feedback
4. Thickness: 2-3mm for best sensitivity
```

### **Touch Zone Layout**

```
Recommended Touch Zones:

Menu Button:     15mm x 15mm (top-left)
Play Button:     15mm x 15mm (top-right)
Previous:        15mm x 15mm (bottom-left)
Next:            15mm x 15mm (bottom-right)
Select:          20mm x 20mm (center-bottom)
Scroll Area:     30mm x 60mm (sides, optional)
```

## 🔧 **Assembly Instructions**

### **Step 1: Prepare Touch Pads**
```
Using Copper Tape:
1. Cut 15mm x 15mm squares
2. Stick inside case at marked positions
3. Solder thin wire to each pad
4. Route wires to TTP229 location
5. Secure with hot glue or tape
```

### **Step 2: Connect TTP229**
```
1. Mount TTP229 module inside case
2. Connect power (3.3V, GND)
3. Connect I2C (SDA, SCL) to ESP32-S3
4. Solder touch pad wires to TP0-TP8
5. Test each pad before closing case
```

### **Step 3: Calibration**
```
1. Power on with no touch
2. TTP229 auto-calibrates (2 seconds)
3. Test each touch zone
4. Adjust sensitivity if needed:
   - Too sensitive: Increase plastic thickness
   - Not sensitive: Larger pads or thinner plastic
```

## 🎯 **Advantages Over Other Methods**

### **vs Physical Buttons**
```
✅ No button holes in case (waterproof)
✅ No mechanical wear
✅ Sleek, modern appearance
✅ Easier case design
✅ More reliable long-term
```

### **vs Resistive Touch Screen**
```
✅ Works through case material
✅ No calibration issues
✅ Better for music player (no accidental touches)
✅ Cheaper than touch display
✅ Lower power consumption
```

### **vs Haptic Buttons**
```
✅ No DRV2605L needed (simpler)
✅ No LRA needed (cheaper)
✅ Fewer components
✅ Can add haptic later if desired
```

## 💰 **Cost Comparison**

```
TTP229 Solution:
- TTP229 module: $5 (₹400)
- Copper tape: $2 (₹150)
- Wires: $1 (₹80)
Total: $8 (₹630)

vs Haptic Solution:
- DRV2605L: $15 (₹1200)
- LRA: $8 (₹600)
- Tactile buttons: $2 (₹160)
Total: $25 (₹1960)

Savings: $17 (₹1330) 💰
```

This TTP229 solution is **perfect for your iPod project** - it's cheaper, simpler, and gives you that modern touch-sensitive interface without needing physical buttons or expensive haptic drivers!

Would you like me to create the complete iPod interface code with TTP229 integration?
