Stavin13/DIY--Ipod-with-esp32-board/pcb/kicad_tutorial.md

# KiCad PCB Design Tutorial - ESP32-S3 iPod Project

## 🎯 **Complete Step-by-Step Guide**

This tutorial will walk you through creating the PCB for your ESP32-S3 haptic iPod project using KiCad (free PCB design software).

## 📥 **Step 1: Install KiCad**

### **Download and Install**
```
1. Go to: https://www.kicad.org/download/
2. Download KiCad for your OS (Windows/Mac/Linux)
3. Install with default settings
4. Launch KiCad Project Manager
```

### **First Launch Setup**
```
1. KiCad will create default libraries
2. Configure paths (usually automatic)
3. Set up symbol and footprint libraries
4. Update libraries if prompted
```

## 🗂️ **Step 2: Create New Project**

### **Project Setup**
```
1. File → New Project
2. Name: "ESP32_iPod_Haptic"
3. Location: Choose your project folder
4. Click "Create Project"
```

### **Project Structure**
```
ESP32_iPod_Haptic/
├── ESP32_iPod_Haptic.kicad_pro    (Project file)
├── ESP32_iPod_Haptic.kicad_sch    (Schematic)
├── ESP32_iPod_Haptic.kicad_pcb    (PCB layout)
├── libraries/                      (Custom libraries)
└── gerbers/                       (Manufacturing files)
```

## 📋 **Step 3: Schematic Design**

### **Open Schematic Editor**
```
1. Double-click "ESP32_iPod_Haptic.kicad_sch"
2. Schematic Editor opens
3. Set up page settings:
   - File → Page Settings
   - Title: "ESP32-S3 iPod Haptic Feedback"
   - Size: A4
   - Add your name and date
```

### **Add Components**

#### **Power Supply Section**
```
1. Press 'A' (Add Symbol)
2. Search and add:
   - "Regulator_Linear:AMS1117-3.3" (U2)
   - "power:+5V" (power symbol)
   - "power:+3V3" (power symbol)  
   - "power:GND" (power symbol)
   - "Device:C" for capacitors (C1, C2)

3. Place components logically:
   - +5V input on left
   - Regulator in middle
   - +3V3 output on right
   - Capacitors near regulator
```

#### **ESP32-S3 Module**
```
1. Add Symbol: Search "ESP32-S3"
2. If not found, use generic microcontroller:
   - "MCU_Espressif:ESP32-S3-WROOM-1" 
   - Or create custom symbol with 41 pins
3. Place in center-left of schematic
4. Add power connections (+3V3, GND)
```

#### **Display Interface**
```
1. Add connector: "Connector:Conn_01x09_Male" (J1)
2. Label pins:
   - Pin 1: GND
   - Pin 2: +3V3 (VCC)
   - Pin 3: +3V3 (LED)
   - Pin 4: TFT_RST
   - Pin 5: TFT_DC
   - Pin 6: TFT_CS
   - Pin 7: SPI_MOSI
   - Pin 8: SPI_CLK
   - Pin 9: SPI_MISO
```

#### **Haptic Driver**
```
1. Add DRV2605L:
   - Search "DRV2605L" or use generic IC
   - Or add "Connector:Conn_01x06_Male" for breakout
2. Add LRA connector: "Connector:Conn_01x02_Male" (J3)
3. Connect I2C lines (SDA, SCL)
```

#### **Button Interface**
```
1. Add 4x tactile switches:
   - "Switch:SW_Push" (SW1-SW4)
2. Add pull-up resistors:
   - "Device:R" (R1-R4, 10kΩ)
3. Connect to ESP32-S3 GPIOs
```

### **Wire Connections**
```
1. Press 'W' (Wire tool)
2. Click to start wire, click to end
3. Connect all components according to schematic
4. Use net labels for long connections:
   - Press 'L' (Add Label)
   - Name: "I2C_SDA", "SPI_MOSI", etc.
```

### **Add Component Values**
```
1. Select component (click on it)
2. Press 'E' (Edit properties)
3. Set Value field:
   - R1-R4: "10k"
   - C1: "220uF"
   - C2: "100uF"
   - U2: "AMS1117-3.3"
```

### **Electrical Rules Check (ERC)**
```
1. Tools → Electrical Rules Checker
2. Click "Run ERC"
3. Fix any errors or warnings:
   - Unconnected pins
   - Power not driven
   - Conflicting drivers
4. Save schematic (Ctrl+S)
```

## 🔧 **Step 4: PCB Layout**

### **Open PCB Editor**
```
1. Tools → Update PCB from Schematic (F8)
2. Click "Update PCB"
3. All components appear in PCB editor
4. Components will be in a pile - need to arrange
```

### **Set Up PCB**

#### **Board Outline**
```
1. Select "Edge.Cuts" layer
2. Use "Draw Rectangle" tool
3. Draw 100mm x 60mm rectangle
4. This defines your PCB boundary
```

#### **Design Rules**
```
1. File → Board Setup
2. Design Rules → Net Classes:
   - Default: 0.2mm trace, 0.2mm clearance
   - Power: 0.5mm trace, 0.2mm clearance
3. Design Rules → Constraints:
   - Minimum track width: 0.15mm
   - Minimum via size: 0.2mm
   - Minimum hole size: 0.1mm
```

### **Component Placement**

#### **Placement Strategy**
```
1. ESP32-S3: Center-left of board
2. DRV2605L: Near ESP32-S3 (short I2C traces)
3. Buttons: Four corners for case mounting
4. Connectors: Board edges
5. Power components: Near power input
```

#### **Placement Process**
```
1. Select component
2. Press 'M' (Move) or drag
3. Press 'R' (Rotate) to rotate
4. Press 'F' (Flip) to flip to bottom layer
5. Arrange logically before routing
```

### **Routing**

#### **Auto-Router Setup**
```
1. Route → Route Tracks (X key)
2. Or use auto-router:
   - Tools → External Plugins → FreeRouting
   - Export DSN file
   - Import back after routing
```

#### **Manual Routing (Recommended)**
```
1. Start with power traces (wide, 0.5mm)
2. Route critical signals (clocks, resets)
3. Route remaining signals
4. Keep traces short and direct
5. Avoid 90° angles (use 45°)
```

#### **Layer Usage**
```
Top Layer (F.Cu):
- Component placement
- Signal traces
- Power traces

Bottom Layer (B.Cu):
- Ground plane (mostly)
- Some signal traces
- Return paths
```

### **Ground Plane**
```
1. Select bottom layer (B.Cu)
2. Tools → Fill Zones
3. Draw zone covering entire board
4. Net: GND
5. Fill type: Solid
6. Thermal relief for pads
```

### **Design Rule Check (DRC)**
```
1. Tools → Design Rules Checker
2. Click "Run DRC"
3. Fix violations:
   - Trace too close to pad
   - Via too close to trace
   - Clearance violations
4. Re-run until clean
```

## 🎨 **Step 5: Finishing Touches**

### **Silkscreen Labels**
```
1. Select F.SilkS layer
2. Add text labels:
   - Component references (U1, R1, etc.)
   - Pin 1 indicators
   - Connector labels
   - Version number
   - Your name/logo
```

### **Solder Mask**
```
1. Solder mask automatically generated
2. Adjust if needed:
   - Expose test points
   - Cover sensitive traces
   - Custom openings
```

### **3D Visualization**
```
1. View → 3D Viewer
2. Check component placement
3. Verify connector orientations
4. Look for mechanical conflicts
5. Take screenshots for documentation
```

## 📦 **Step 6: Generate Manufacturing Files**

### **Gerber Files**
```
1. File → Plot
2. Select all layers:
   - F.Cu (Top copper)
   - B.Cu (Bottom copper)
   - F.SilkS (Top silkscreen)
   - B.SilkS (Bottom silkscreen)
   - F.Mask (Top solder mask)
   - B.Mask (Bottom solder mask)
   - Edge.Cuts (Board outline)
3. Output directory: "gerbers/"
4. Format: Gerber (RS-274X)
5. Click "Plot"
```

### **Drill Files**
```
1. Click "Generate Drill Files"
2. Format: Excellon
3. Units: Millimeters
4. Zeros: Suppress leading zeros
5. Click "Generate Drill File"
```

### **Pick and Place Files**
```
1. File → Fabrication Outputs
2. Component Placement (.pos)
3. Format: CSV
4. Units: Millimeters
5. Include only SMD components
```

### **Bill of Materials (BOM)**
```
1. Tools → Generate BOM
2. Select BOM plugin
3. Generate CSV file
4. Include:
   - Reference designator
   - Value
   - Footprint
   - Quantity
   - Supplier part number
```

## 📋 **Step 7: Manufacturing Preparation**

### **File Organization**
```
gerbers/
├── ESP32_iPod_Haptic-F_Cu.gbr      (Top copper)
├── ESP32_iPod_Haptic-B_Cu.gbr      (Bottom copper)
├── ESP32_iPod_Haptic-F_SilkS.gbr   (Top silkscreen)
├── ESP32_iPod_Haptic-B_SilkS.gbr   (Bottom silkscreen)
├── ESP32_iPod_Haptic-F_Mask.gbr    (Top solder mask)
├── ESP32_iPod_Haptic-B_Mask.gbr    (Bottom solder mask)
├── ESP32_iPod_Haptic-Edge_Cuts.gbr (Board outline)
├── ESP32_iPod_Haptic-NPTH.drl      (Non-plated holes)
├── ESP32_iPod_Haptic-PTH.drl       (Plated holes)
└── ESP32_iPod_Haptic-all.zip       (Zip for upload)
```

### **Gerber Verification**
```
1. Use online Gerber viewer:
   - gerber-viewer.org
   - pcbway.com/project/OnlineGerberViewer.html
2. Check all layers load correctly
3. Verify board dimensions
4. Check drill holes align
```

### **Upload to Manufacturer**
```
1. Create ZIP file with all Gerbers
2. Upload to JLCPCB/PCBWay
3. Review PCB preview
4. Select options:
   - Quantity: 5 pieces
   - Thickness: 1.6mm
   - Color: Green (cheapest)
   - Surface finish: HASL
5. Add to cart and order
```

## 🔧 **Step 8: Assembly Preparation**

### **Assembly Drawings**
```
1. File → Plot
2. Select F.Fab layer
3. Generate assembly drawing
4. Add component values and references
5. Create both top and bottom views
```

### **Stencil (Optional)**
```
For SMD assembly:
1. File → Plot
2. Select F.Paste layer
3. Generate stencil Gerber
4. Order stencil from manufacturer
5. Use for solder paste application
```

## 🎯 **Common Beginner Mistakes to Avoid**

### **Schematic Errors**
```
❌ Forgetting power connections
❌ Wrong pin assignments
❌ Missing pull-up resistors
❌ Incorrect component values
❌ Unconnected nets

✅ Always run ERC
✅ Double-check pin assignments
✅ Verify component datasheets
✅ Use net labels for clarity
```

### **PCB Layout Errors**
```
❌ Components too close together
❌ Traces too thin for current
❌ No ground plane
❌ Poor component placement
❌ 90° trace angles

✅ Follow design rules
✅ Keep high-speed traces short
✅ Use ground plane
✅ Plan component placement first
✅ Run DRC frequently
```

### **Manufacturing Issues**
```
❌ Wrong drill sizes
❌ Missing layers in Gerber
❌ Incorrect board dimensions
❌ Text too small to read
❌ Vias in pads

✅ Verify Gerber files
✅ Check drill file alignment
✅ Use standard dimensions
✅ Make text ≥0.15mm high
✅ Avoid vias in SMD pads
```

## 📚 **Learning Resources**

### **KiCad Documentation**
```
Official Tutorial: docs.kicad.org/master/en/getting_started_in_kicad/
Video Tutorials: YouTube "KiCad tutorial"
Community: forum.kicad.info
Examples: github.com/KiCad (example projects)
```

### **PCB Design Guidelines**
```
IPC Standards: PCB design rules
Saturn PCB Toolkit: Trace width calculator
Signal Integrity: High-speed design rules
Thermal Management: Power dissipation
```

## ⏱️ **Time Estimates**

### **Learning Phase**
```
KiCad basics: 2-3 days
First simple PCB: 1 week
iPod project PCB: 2-3 days (after learning)
```

### **Design Phase**
```
Schematic design: 4-6 hours
Component placement: 2-3 hours
Routing: 4-8 hours
Verification and cleanup: 2-3 hours
Manufacturing files: 1 hour

Total: 2-3 days for complete PCB
```

### **Manufacturing**
```
PCB fabrication: 2-3 days (JLCPCB)
Shipping: 7-15 days (international)
Assembly: 2-4 hours (hand soldering)
Testing: 1-2 hours
```

## 🎯 **Success Tips**

### **Start Simple**
```
1. Practice with LED blinker circuit first
2. Learn schematic symbols and footprints
3. Understand layer stack-up
4. Master basic routing techniques
5. Then tackle complex projects
```

### **Use Resources**
```
1. KiCad built-in libraries (comprehensive)
2. SnapEDA.com (free footprints)
3. Ultra Librarian (manufacturer libraries)
4. GitHub KiCad libraries (community)
5. Component datasheets (always check)
```

### **Verify Everything**
```
1. Print PCB at 1:1 scale, check component fit
2. Use online Gerber viewers
3. Get second opinion on design
4. Order extra PCBs (mistakes happen)
5. Test with breadboard first
```

This tutorial will get you from zero to a professional PCB for your haptic iPod project! Take your time with each step, and don't hesitate to practice with simpler circuits first. 🚀

The end result will be a clean, professional PCB that's much more reliable than breadboard prototypes and ready for production!

Would you like me to create the actual KiCad project files to get you started?
