Stavin13/DIY--Ipod-with-esp32-board/src/wiring_verification_test.cpp

/*
Wiring Verification Test
Tests each pin individually to verify connections
Upload this to check if your wiring is correct
*/

#include <TFT_eSPI.h>

TFT_eSPI tft = TFT_eSPI();

// Pin definitions
#define TOUCH_CS  6     // Touch Chip Select
#define TOUCH_CLK 7     // Touch Clock  
#define TOUCH_DIN 5     // Touch Data In
#define TOUCH_DO  4     // Touch Data Out
#define TOUCH_IRQ 3     // Touch Interrupt

void setup() {
  Serial.begin(115200);
  delay(3000);
  
  Serial.println("╔════════════════════════════════════════╗");
  Serial.println("║        Wiring Verification Test       ║");
  Serial.println("║         Pin-by-Pin Check v1.0         ║");
  Serial.println("╚════════════════════════════════════════╝");
  Serial.println();
  
  // Initialize display
  tft.init();
  tft.setRotation(0);
  tft.fillScreen(TFT_BLACK);
  
  tft.setTextSize(2);
  tft.setTextColor(TFT_WHITE);
  tft.setCursor(20, 20);
  tft.println("Wiring Test");
  
  Serial.println("🔌 EXPECTED WIRING:");
  Serial.println("   ESP32-S3    MSP2806");
  Serial.println("   --------    -------");
  Serial.println("   GPIO10  →   CS");
  Serial.println("   GPIO9   →   DC");
  Serial.println("   GPIO8   →   RST");
  Serial.println("   GPIO11  →   SDA/MOSI");
  Serial.println("   GPIO12  →   SCL/SCLK");
  Serial.println("   GPIO13  →   SDO/MISO");
  Serial.println("   3.3V    →   VCC");
  Serial.println("   3.3V    →   LED");
  Serial.println("   GND     →   GND");
  Serial.println("   GPIO6   →   T_CS");
  Serial.println("   GPIO7   →   T_CLK");
  Serial.println("   GPIO5   →   T_DIN");
  Serial.println("   GPIO4   →   T_DO");
  Serial.println("   GPIO3   →   T_IRQ");
  Serial.println();
  
  Serial.println("🧪 TESTING EACH PIN:");
  Serial.println();
  
  testDisplayPins();
  testTouchPins();
  testPowerConnections();
  
  Serial.println("🔍 TOUCH CONTROLLER TEST:");
  testTouchController();
  
  Serial.println("\n📋 FINAL RECOMMENDATIONS:");
  provideFinalRecommendations();
}

void loop() {
  // Continuous monitoring
  monitorTouch();
  delay(500);
}

void testDisplayPins() {
  Serial.println("📺 DISPLAY PINS TEST:");
  
  // Test if display is working (we can see it)
  Serial.println("   ✅ Display is working (you can see this text)");
  
  // Test display SPI pins by drawing
  tft.setTextSize(1);
  tft.setTextColor(TFT_GREEN);
  tft.setCursor(10, 60);
  tft.println("Display SPI: OK");
  
  Serial.println("   ✅ Display SPI communication working");
  Serial.println("   ✅ TFT_CS (GPIO10) working");
  Serial.println("   ✅ TFT_DC (GPIO9) working");
  Serial.println("   ✅ TFT_RST (GPIO8) working");
  Serial.println("   ✅ TFT_MOSI (GPIO11) working");
  Serial.println("   ✅ TFT_SCLK (GPIO12) working");
  Serial.println();
}

void testTouchPins() {
  Serial.println("👆 TOUCH PINS TEST:");
  
  // Configure touch pins
  pinMode(TOUCH_CS, OUTPUT);
  pinMode(TOUCH_CLK, OUTPUT);
  pinMode(TOUCH_DIN, OUTPUT);
  pinMode(TOUCH_DO, INPUT);
  pinMode(TOUCH_IRQ, INPUT_PULLUP);
  
  // Test CS pin
  digitalWrite(TOUCH_CS, HIGH);
  delay(1);
  bool csHigh = digitalRead(TOUCH_CS);
  digitalWrite(TOUCH_CS, LOW);
  delay(1);
  bool csLow = digitalRead(TOUCH_CS);
  
  Serial.print("   TOUCH_CS (GPIO6): ");
  if (csHigh && !csLow) {
    Serial.println("✅ Working");
  } else {
    Serial.println("❌ Not responding");
  }
  
  // Test CLK pin
  digitalWrite(TOUCH_CLK, HIGH);
  delay(1);
  digitalWrite(TOUCH_CLK, LOW);
  Serial.println("   TOUCH_CLK (GPIO7): ✅ Configured as output");
  
  // Test DIN pin
  digitalWrite(TOUCH_DIN, HIGH);
  delay(1);
  digitalWrite(TOUCH_DIN, LOW);
  Serial.println("   TOUCH_DIN (GPIO5): ✅ Configured as output");
  
  // Test DO pin
  Serial.print("   TOUCH_DO (GPIO4): ");
  int doState = digitalRead(TOUCH_DO);
  Serial.print("Reading ");
  Serial.print(doState ? "HIGH" : "LOW");
  Serial.println(" ✅ Configured as input");
  
  // Test IRQ pin
  Serial.print("   TOUCH_IRQ (GPIO3): ");
  int irqState = digitalRead(TOUCH_IRQ);
  Serial.print("Reading ");
  Serial.print(irqState ? "HIGH" : "LOW");
  if (irqState) {
    Serial.println(" ✅ (Good - pulled HIGH)");
  } else {
    Serial.println(" ⚠️  (Should be HIGH with pullup)");
  }
  
  Serial.println();
}

void testPowerConnections() {
  Serial.println("⚡ POWER CONNECTIONS TEST:");
  
  // We can't directly test power, but we can infer
  Serial.println("   ✅ 3.3V to display VCC (display is working)");
  Serial.println("   ✅ 3.3V to display LED (backlight is on)");
  Serial.println("   ✅ GND connections (display is working)");
  
  // Check if touch controller has power by testing communication
  digitalWrite(TOUCH_CS, LOW);
  delayMicroseconds(10);
  
  // Send a command
  uint8_t command = 0x90; // Read X
  for (int i = 7; i >= 0; i--) {
    digitalWrite(TOUCH_DIN, (command >> i) & 1);
    delayMicroseconds(1);
    digitalWrite(TOUCH_CLK, HIGH);
    delayMicroseconds(1);
    digitalWrite(TOUCH_CLK, LOW);
    delayMicroseconds(1);
  }
  
  // Try to read response
  uint16_t response = 0;
  for (int i = 0; i < 12; i++) {
    digitalWrite(TOUCH_CLK, HIGH);
    delayMicroseconds(1);
    response = (response << 1) | digitalRead(TOUCH_DO);
    digitalWrite(TOUCH_CLK, LOW);
    delayMicroseconds(1);
  }
  
  digitalWrite(TOUCH_CS, HIGH);
  
  Serial.print("   Touch controller power test: ");
  if (response > 0 && response < 0xFFF) {
    Serial.println("✅ Touch controller has power and responds");
  } else if (response == 0) {
    Serial.println("❌ No response - check 3.3V to touch controller");
  } else {
    Serial.println("⚠️  Unexpected response - check connections");
  }
  
  Serial.println();
}

void testTouchController() {
  Serial.println("🎯 Testing XPT2046 touch controller communication...");
  
  // Test multiple commands
  uint16_t xVal = readTouchCommand(0x90); // X coordinate
  uint16_t yVal = readTouchCommand(0xD0); // Y coordinate
  uint16_t z1Val = readTouchCommand(0xB0); // Z1 pressure
  uint16_t z2Val = readTouchCommand(0xC0); // Z2 pressure
  
  Serial.print("   Raw values: X=");
  Serial.print(xVal);
  Serial.print(" Y=");
  Serial.print(yVal);
  Serial.print(" Z1=");
  Serial.print(z1Val);
  Serial.print(" Z2=");
  Serial.println(z2Val);
  
  // Analyze the results
  if (xVal == 0 && yVal == 0 && z1Val == 0 && z2Val == 0) {
    Serial.println("   ❌ All readings are 0 - touch controller not responding");
    Serial.println("      Check: 3.3V power, GND, and all touch pin connections");
  } else if (xVal == 0xFFF && yVal == 0xFFF) {
    Serial.println("   ❌ All readings are maximum - pins stuck HIGH");
    Serial.println("      Check: Touch pin connections, especially T_DO");
  } else if (xVal > 100 && xVal < 4000 && yVal > 100 && yVal < 4000) {
    Serial.println("   ✅ Touch controller responding with valid data!");
    Serial.println("      Hardware is working - issue is likely software configuration");
  } else {
    Serial.println("   ⚠️  Touch controller responding but values seem unusual");
    Serial.println("      Try touching the screen firmly while testing");
  }
  
  // Display results on screen
  tft.setTextSize(1);
  tft.setTextColor(TFT_YELLOW);
  tft.setCursor(10, 100);
  tft.print("Touch Test:");
  tft.setCursor(10, 120);
  tft.print("X=");
  tft.print(xVal);
  tft.print(" Y=");
  tft.print(yVal);
  
  if (xVal > 100 && xVal < 4000 && yVal > 100 && yVal < 4000) {
    tft.setTextColor(TFT_GREEN);
    tft.setCursor(10, 140);
    tft.println("Hardware OK!");
  } else {
    tft.setTextColor(TFT_RED);
    tft.setCursor(10, 140);
    tft.println("Check wiring");
  }
}

uint16_t readTouchCommand(uint8_t command) {
  digitalWrite(TOUCH_CS, LOW);
  delayMicroseconds(10);
  
  // Send 8-bit command
  for (int i = 7; i >= 0; i--) {
    digitalWrite(TOUCH_DIN, (command >> i) & 1);
    delayMicroseconds(1);
    digitalWrite(TOUCH_CLK, HIGH);
    delayMicroseconds(1);
    digitalWrite(TOUCH_CLK, LOW);
    delayMicroseconds(1);
  }
  
  // Read 12-bit response
  uint16_t result = 0;
  for (int i = 0; i < 12; i++) {
    digitalWrite(TOUCH_CLK, HIGH);
    delayMicroseconds(1);
    result = (result << 1) | digitalRead(TOUCH_DO);
    digitalWrite(TOUCH_CLK, LOW);
    delayMicroseconds(1);
  }
  
  digitalWrite(TOUCH_CS, HIGH);
  delayMicroseconds(10);
  
  return result;
}

void provideFinalRecommendations() {
  uint16_t testX = readTouchCommand(0x90);
  uint16_t testY = readTouchCommand(0xD0);
  
  if (testX == 0 && testY == 0) {
    Serial.println("❌ HARDWARE ISSUE - Touch controller not responding");
    Serial.println("   1. Double-check ALL touch pin connections:");
    Serial.println("      ESP32-S3 GPIO6 → MSP2806 T_CS");
    Serial.println("      ESP32-S3 GPIO7 → MSP2806 T_CLK");
    Serial.println("      ESP32-S3 GPIO5 → MSP2806 T_DIN");
    Serial.println("      ESP32-S3 GPIO4 → MSP2806 T_DO");
    Serial.println("      ESP32-S3 GPIO3 → MSP2806 T_IRQ");
    Serial.println("   2. Verify 3.3V power to touch controller");
    Serial.println("   3. Check GND connections");
    Serial.println("   4. Try different jumper wires");
    Serial.println("   5. Push breadboard connections firmly");
  } else if (testX > 100 && testX < 4000) {
    Serial.println("✅ HARDWARE IS WORKING!");
    Serial.println("   Touch controller responds correctly.");
    Serial.println("   Issue is likely software configuration:");
    Serial.println("   1. Upload user_setup_checker.cpp to verify User_Setup.h");
    Serial.println("   2. Make sure SUPPORT_TOUCH is defined");
    Serial.println("   3. Copy User_Setup_Complete.h to TFT_eSPI/User_Setup.h");
    Serial.println("   4. Restart Arduino IDE after changing User_Setup.h");
  } else {
    Serial.println("⚠️  PARTIAL HARDWARE ISSUE");
    Serial.println("   Touch controller responds but values are unusual:");
    Serial.println("   1. Check connection quality (loose wires?)");
    Serial.println("   2. Try touching screen firmly during test");
    Serial.println("   3. Check for electrical interference");
    Serial.println("   4. Verify power supply stability");
  }
  
  Serial.println("\n🔄 NEXT STEPS:");
  Serial.println("1. Fix any hardware issues found above");
  Serial.println("2. Upload user_setup_checker.cpp");
  Serial.println("3. Upload touch_hardware_diagnostic.cpp");
  Serial.println("4. If all tests pass, upload ipod_ui_integrated.cpp");
}

void monitorTouch() {
  static int count = 0;
  count++;
  
  uint16_t x = readTouchCommand(0x90);
  uint16_t y = readTouchCommand(0xD0);
  
  // Only print if there's significant activity
  if (x > 500 || y > 500 || count % 10 == 0) {
    Serial.print("Monitor ");
    Serial.print(count);
    Serial.print(": X=");
    Serial.print(x);
    Serial.print(" Y=");
    Serial.println(y);
    
    // Update display
    tft.fillRect(10, 160, 220, 40, TFT_BLACK);
    tft.setTextSize(1);
    tft.setTextColor(TFT_WHITE);
    tft.setCursor(10, 160);
    tft.print("Live: X=");
    tft.print(x);
    tft.print(" Y=");
    tft.print(y);
    
    if (x > 500 && y > 500) {
      tft.setTextColor(TFT_GREEN);
      tft.setCursor(10, 175);
      tft.println("TOUCH DETECTED!");
    }
  }
}
